stanoba/MIDI2Neopixel/Images/07.jpg

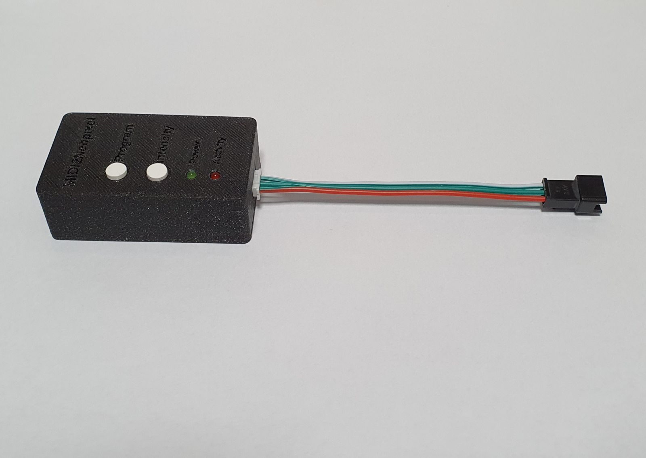
Images/07.jpg
